fionnf/magic-mirror/gallery/2026-10-09.png

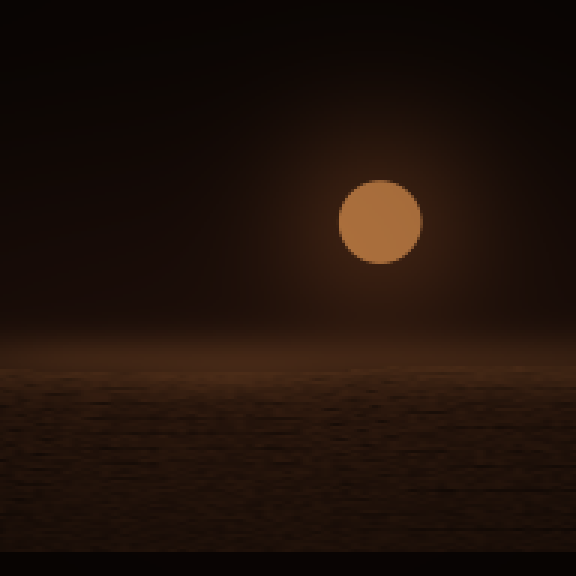
gallery/2026-10-09.png
