fionnf/magic-mirror/hardware/led-wall-frame/images/03_rear_exploded.png

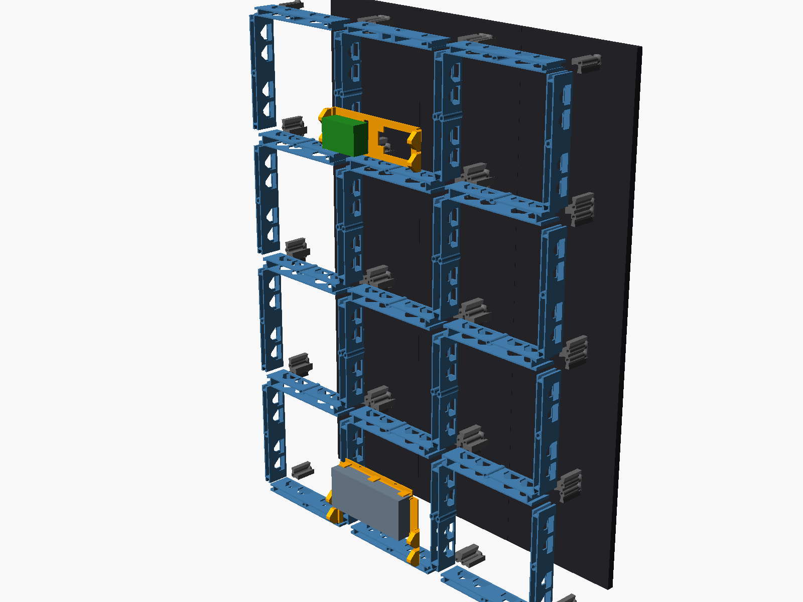
hardware/led-wall-frame/images/03_rear_exploded.png
