fionnf/magic-mirror/hardware/led-wall-frame/images/05_psu_tray.png

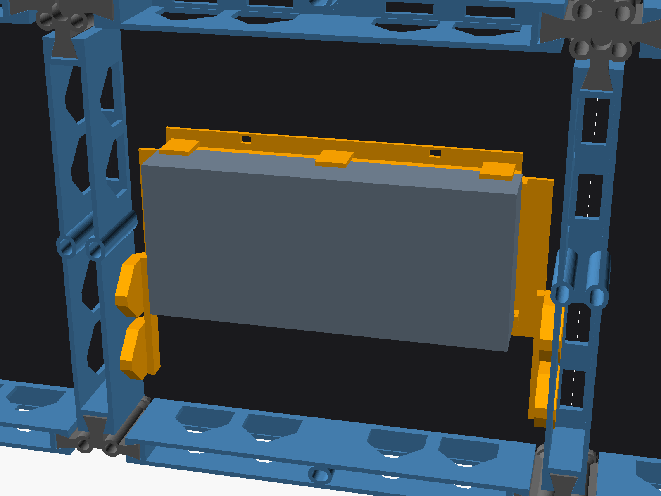
hardware/led-wall-frame/images/05_psu_tray.png
