fionnf/magic-mirror/hardware/led-wall-frame/images/06_camera_module3_pod.png

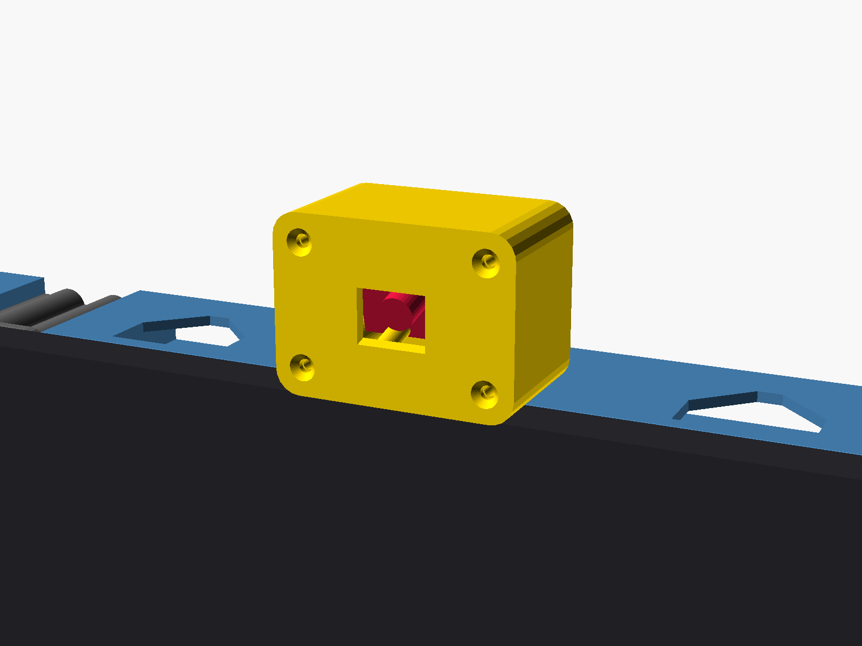
hardware/led-wall-frame/images/06_camera_module3_pod.png
