fionnf/magic-mirror/hardware/led-wall-frame/images/07_c270_box_option.png

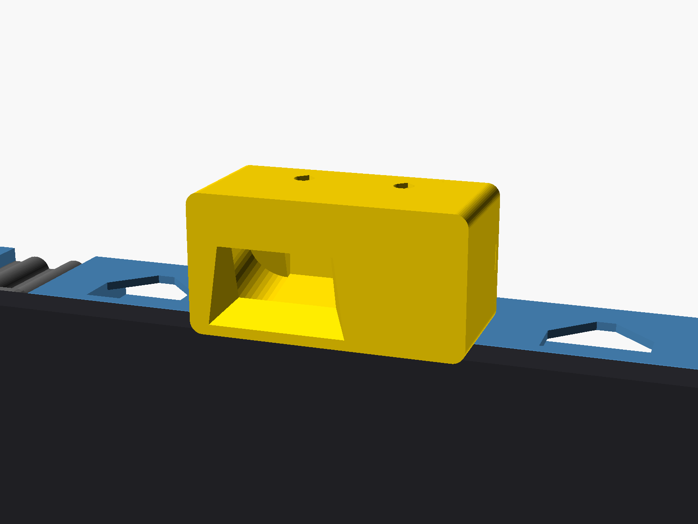
hardware/led-wall-frame/images/07_c270_box_option.png
