fionnf/magic-mirror/hardware/led-wall-frame/images/11_touch_box.png

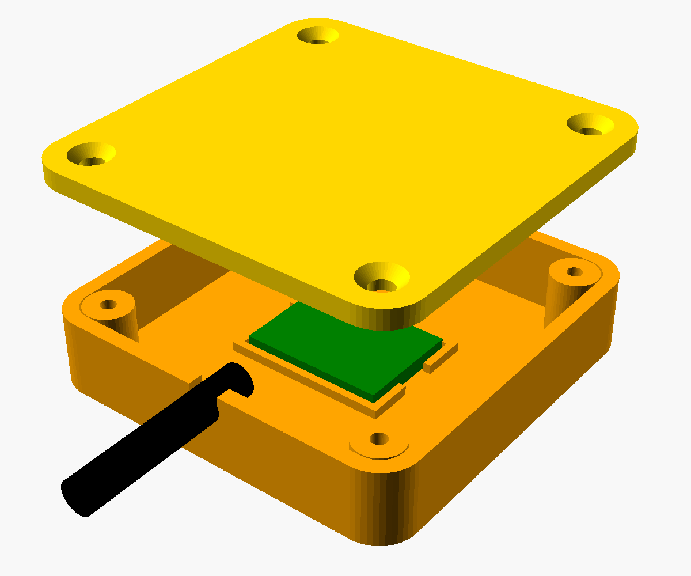
hardware/led-wall-frame/images/11_touch_box.png
