fionnf/magic-mirror/hardware/led-wall-frame/3mf/05_rails_horizontal_x3_outer_x6.3mf

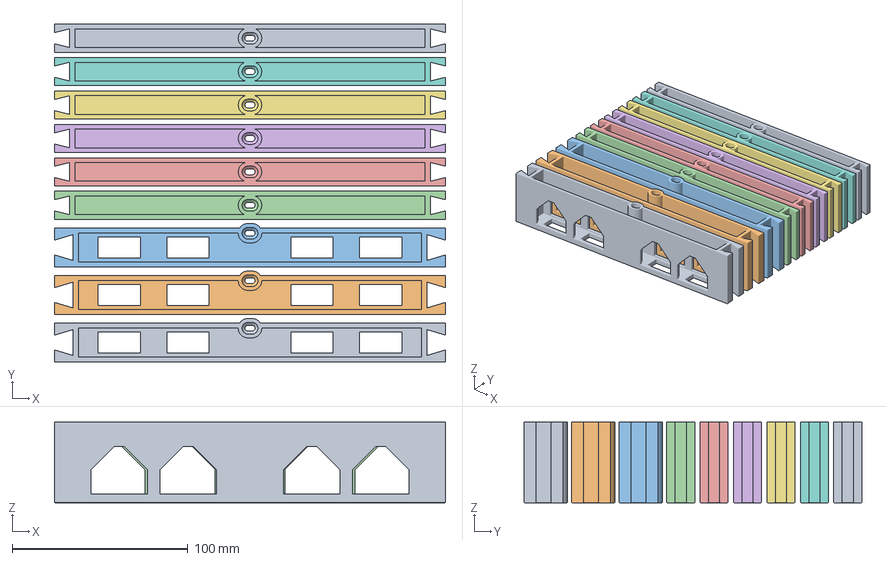
[picture p28: CAD file, 2026-10-09]
hardware/led-wall-frame/3mf/05_rails_horizontal_x3_outer_x6.3mf
222.2 x 192.0 x 46.0 mm
rail 1
rail 2
rail 3
rail 4
rail 5
rail 6
rail 7
rail 8
rail 9
